shashwtd/boardstorm-x3/images/pcb-render-back.png

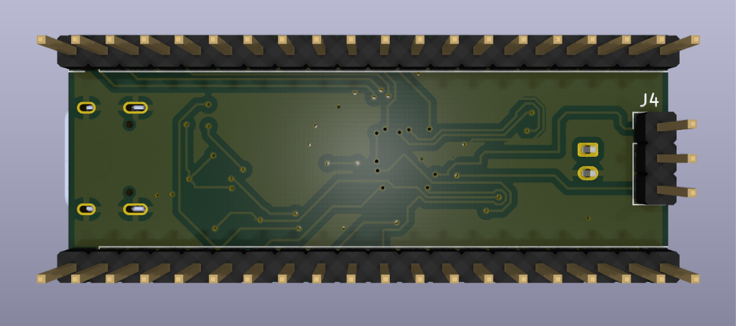
images/pcb-render-back.png
